Batterhead221/pocket_sprite/Outputs/IMG/L1.png

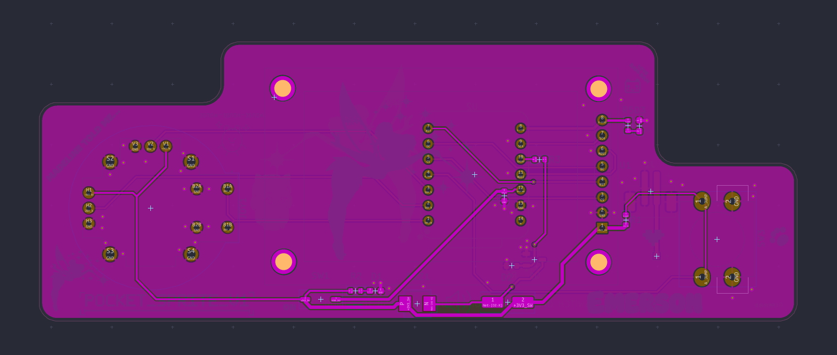
Outputs/IMG/L1.png
