Batterhead221/pocket_sprite/Outputs/IMG/L2.png

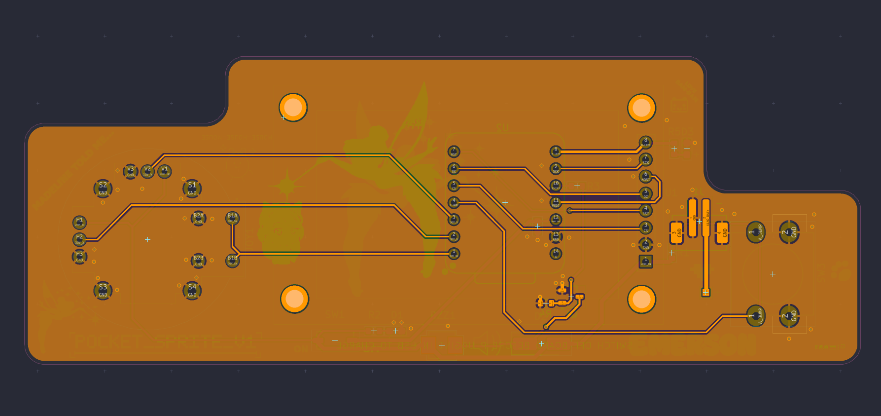
Outputs/IMG/L2.png
