Batterhead221/pocket_sprite/Outputs/IMG/SCHEMATIC.png

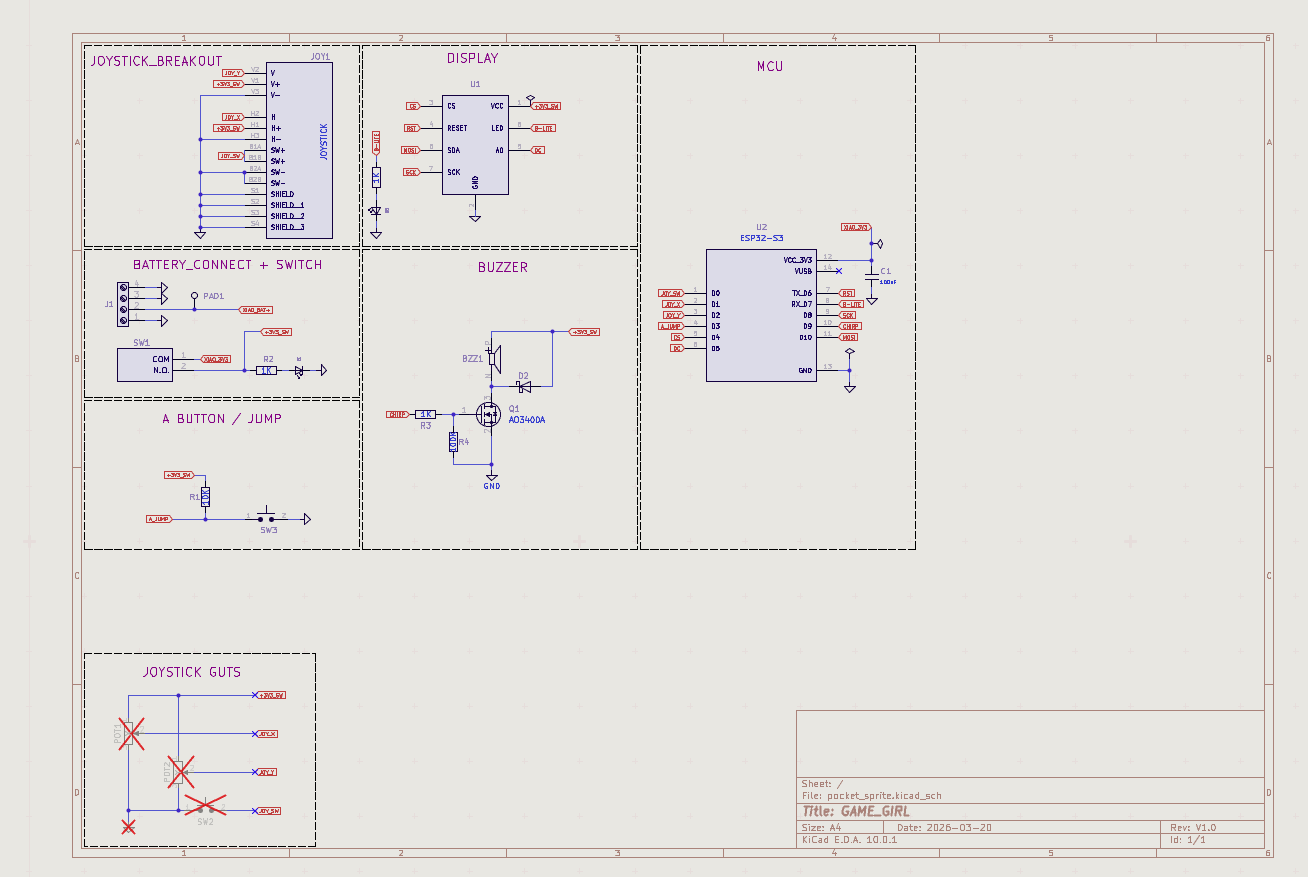
Outputs/IMG/SCHEMATIC.png
